Omgisawsome/stealth-calculator/Schematic/StealthCalculator.kicad_sch

## KiCad design Schematic/StealthCalculator.kicad_sch (2026-04-02)

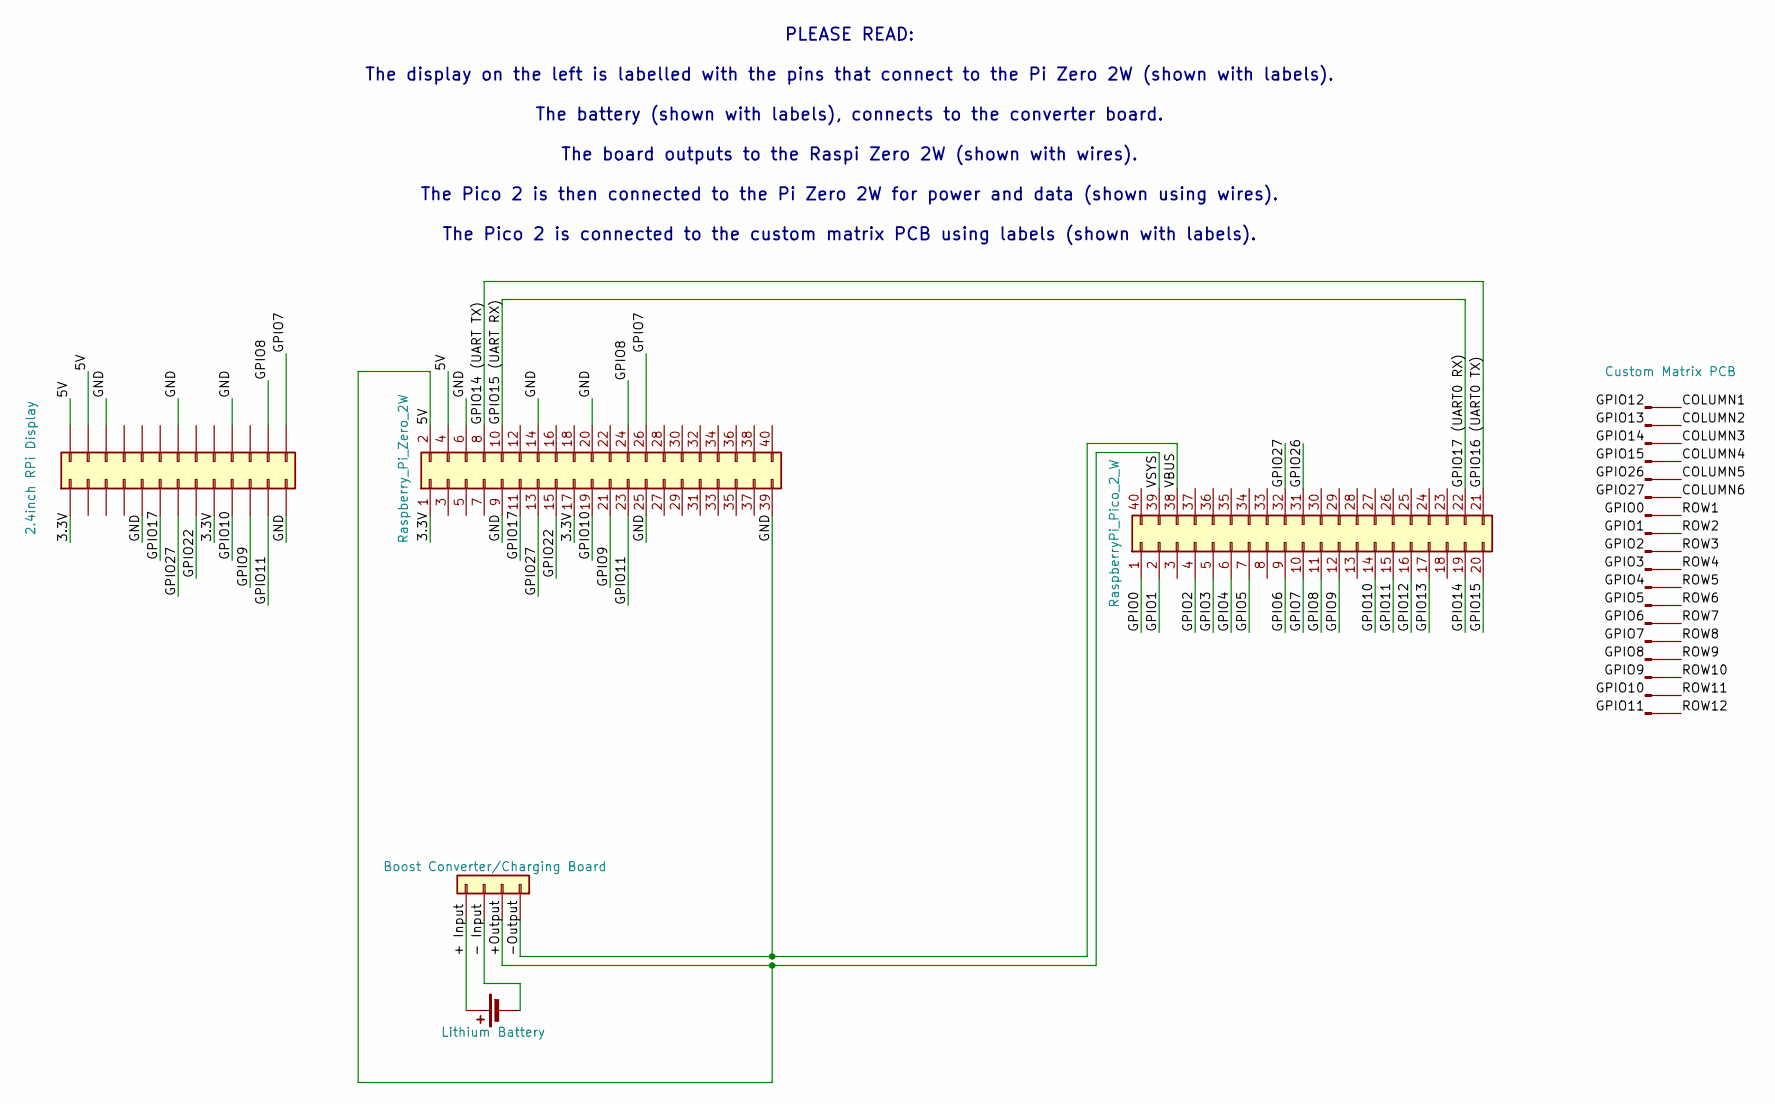
[picture p16: schematic StealthCalculator.kicad_sch]

Parts:
A1: Raspberry_Pi_Zero_2W
B1: 2.4inch RPi Display
BT1: Lithium Battery
J1: RaspberryPi_Pico_2_W
J2: Custom Matrix PCB
J3: Boost Converter/Charging Board

Connections:
3.3V: A1.1, A1.17, B1.1, B1.17
+ Input: BT1.1 (+), J3.4
+Output: A1.2, A1.4, B1.2, B1.4, J1.39, J3.2
- Input: BT1.2 (-), J3.3
-Output: A1.6, A1.9, A1.14, A1.20, A1.25, A1.39, B1.6, B1.9, B1.14, B1.20, B1.25, J1.38, J3.1
COLUMN1: J2.1
COLUMN2: J2.2
COLUMN3: J2.3
COLUMN4: J2.4
COLUMN5: J2.5
COLUMN6: J2.6
GPIO0: J1.1
GPIO1: J1.2
GPIO2: J1.4
GPIO3: J1.5
GPIO4: J1.6
GPIO5: J1.7
GPIO6: J1.9
GPIO7: A1.26, B1.26, J1.10
GPIO8: A1.24, B1.24, J1.11
GPIO9: A1.21, B1.21, J1.12
GPIO10: A1.19, B1.19, J1.14
GPIO11: A1.23, B1.23, J1.15
GPIO12: J1.16
GPIO13: J1.17
GPIO14: J1.19
GPIO14 (UART TX): A1.8, J1.21
GPIO15: J1.20
GPIO15 (UART RX): A1.10, J1.22
GPIO17: A1.11, B1.11
GPIO22: A1.15, B1.15
GPIO26: J1.31
GPIO27: A1.13, B1.13, J1.32
ROW1: J2.7
ROW2: J2.8
ROW3: J2.9
ROW4: J2.10
ROW5: J2.11
ROW6: J2.12
ROW7: J2.13
ROW8: J2.14
ROW9: J2.15
ROW10: J2.16
ROW11: J2.17
ROW12: J2.18

Notes on the sheet:
PLEASE READ: The display on the left is labelled with the pins that connect to the Pi Zero 2W (shown with labels). The battery (shown with labels), connects to the converter board. The board outputs to the Raspi Zero 2W (shown with wires). The Pico 2 is then connected to the Pi Zero 2W for power an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
